Pooky1306/Pelicase-Cyberdeck/keyboard/firmware/11x5/Pin_map_11x5.png

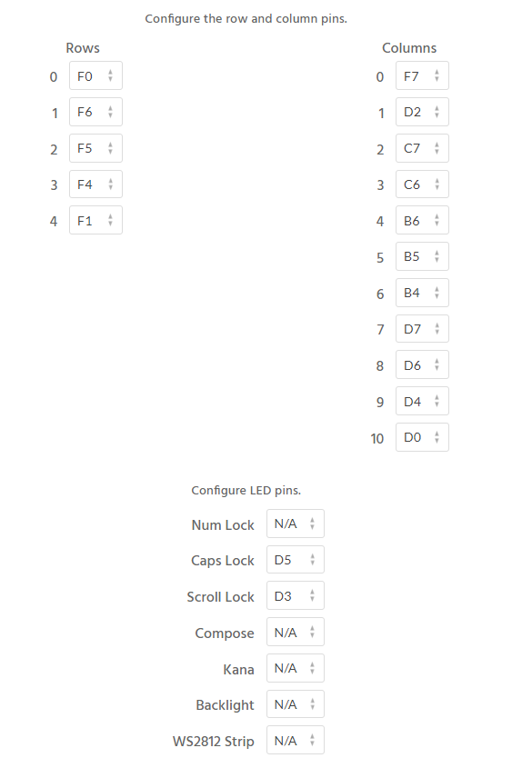
keyboard/firmware/11x5/Pin_map_11x5.png
