Pooky1306/Pelicase-Cyberdeck/keyboard/IMG_20221125_212925 (Large).jpg

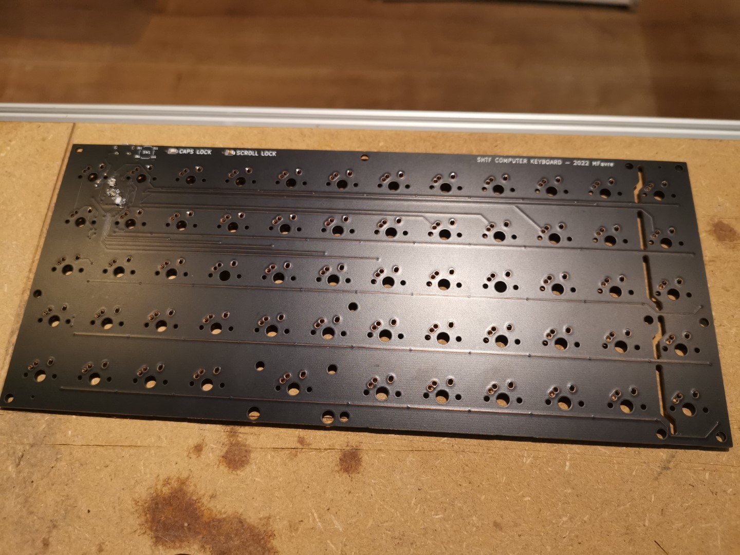
keyboard/IMG_20221125_212925 (Large).jpg
