Pooky1306/Pelicase-Cyberdeck/Peli1150/a4cfbd91-f075-4f76-b617-436ac1e7d497.jpg

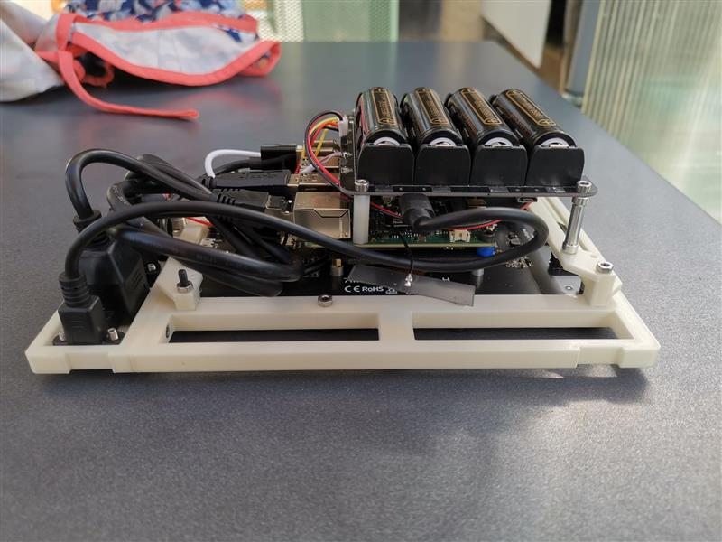
Peli1150/a4cfbd91-f075-4f76-b617-436ac1e7d497.jpg
