Pooky1306/Pelicase-Cyberdeck/Peli1300/keyboard frame/keyboard frame Top.stl

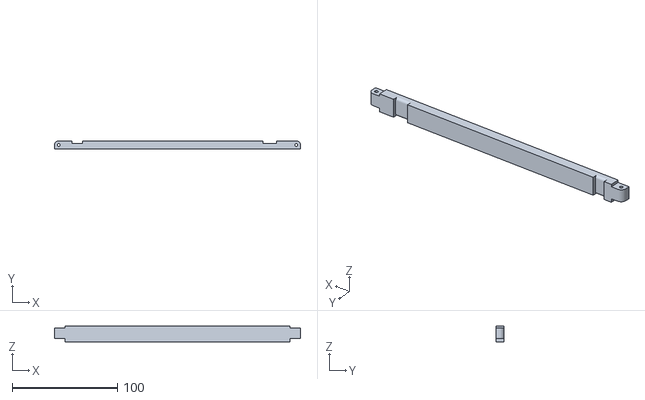
[picture p27: CAD file, 2023-01-11]
Peli1300/keyboard frame/keyboard frame Top.stl
233.3 x 8.00 x 15.0
